sudomesh/disaster-radio/esp8266/esp8266_main.ino

#include <ESP8266WiFi.h>
#include <ESP8266mDNS.h>
#include <ArduinoOTA.h>
#include <FS.h>
#include <Hash.h>
#include <ESPAsyncTCP.h>
#include <ESPAsyncWebServer.h>
#include <SPIFFSEditor.h>
#include <SPI.h>
#include <LoRa.h>

// This is just a slightly modified version of the
// official ESPAsyncWebserver example
// Where SPI has been added to talk to an arduino running the
// arduino_spi_test code

// SKETCH BEGIN
AsyncWebServer server(80);
AsyncWebSocket ws("/ws");
AsyncEventSource events("/events");

void onWsEvent(AsyncWebSocket * server, AsyncWebSocketClient * client, AwsEventType type, void * arg, uint8_t *data, size_t len){
  if(type == WS_EVT_CONNECT){
    Serial.printf("ws[%s][%u] connect\n", server->url(), client->id());
    client->printf("Hello Client %u :)", client->id());
    client->ping();
  } else if(type == WS_EVT_DISCONNECT){
    Serial.printf("ws[%s][%u] disconnect: %u\n", server->url(), client->id());
  } else if(type == WS_EVT_ERROR){
    Serial.printf("ws[%s][%u] error(%u): %s\n", server->url(), client->id(), *((uint16_t*)arg), (char*)data);
  } else if(type == WS_EVT_PONG){
    Serial.printf("ws[%s][%u] pong[%u]: %s\n", server->url(), client->id(), len, (len)?(char*)data:"");
  } else if(type == WS_EVT_DATA){
    AwsFrameInfo * info = (AwsFrameInfo*)arg;
    String msg = "";
    if(info->final && info->index == 0 && info->len == len){
      //the whole message is in a single frame and we got all of it's data
      Serial.printf("ws[%s][%u] %s-message[%llu]: ", server->url(), client->id(), (info->opcode == WS_TEXT)?"text":"binary", info->len);

      if(info->opcode == WS_TEXT){
        for(size_t i=0; i < info->len; i++) {
          msg += (char) data[i];
        }
      } else {
        char buff[3];
        for(size_t i=0; i < info->len; i++) {
          sprintf(buff, "%02x ", (uint8_t) data[i]);
          msg += buff ;
        }
      }
      Serial.printf("%s\n",msg.c_str());

      if(info->opcode == WS_TEXT)
        client->text("I got your text message");
      else
        client->binary("I got your binary message");
    } else {
      //message is comprised of multiple frames or the frame is split into multiple packets
      if(info->index == 0){
        if(info->num == 0)
          Serial.printf("ws[%s][%u] %s-message start\n", server->url(), client->id(), (info->message_opcode == WS_TEXT)?"text":"binary");
        Serial.printf("ws[%s][%u] frame[%u] start[%llu]\n", server->url(), client->id(), info->num, info->len);
      }

      Serial.printf("ws[%s][%u] frame[%u] %s[%llu - %llu]: ", server->url(), client->id(), info->num, (info->message_opcode == WS_TEXT)?"text":"binary", info->index, info->index + len);

      if(info->opcode == WS_TEXT){
        for(size_t i=0; i < info->len; i++) {
          msg += (char) data[i];
        }
      } else {
        char buff[3];
        for(size_t i=0; i < info->len; i++) {
          sprintf(buff, "%02x ", (uint8_t) data[i]);
          msg += buff ;
        }
      }
      Serial.printf("%s\n",msg.c_str());

      if((info->index + len) == info->len){
        Serial.printf("ws[%s][%u] frame[%u] end[%llu]\n", server->url(), client->id(), info->num, info->len);
        if(info->final){
          Serial.printf("ws[%s][%u] %s-message end\n", server->url(), client->id(), (info->message_opcode == WS_TEXT)?"text":"binary");
          if(info->message_opcode == WS_TEXT)
            client->text("I got your text message");
          else
            client->binary("I got your binary message");
        }
      }
    }
  }
}


const char* ssid = "DisasterRadio duino";
//const char* password = "*******";
const char * hostName = "esp-async";
const char* http_username = "admin";
const char* http_password = "admin";

void setup(){
  Serial.begin(115200);
  Serial.setDebugOutput(true);
  WiFi.hostname(hostName);
  //WiFi.mode(WIFI_AP_STA);
  WiFi.mode(WIFI_AP);
  WiFi.softAP(ssid);
  /*
  WiFi.begin(ssid, password);
  if (WiFi.waitForConnectResult() != WL_CONNECTED) {
    Serial.printf("STA: Failed!\n");
    WiFi.disconnect(false);
    delay(1000);
    WiFi.begin(ssid, password);
  }
  */

  //Send OTA events to the browser
  ArduinoOTA.onStart([]() { events.send("Update Start", "ota"); });
  ArduinoOTA.onEnd([]() { events.send("Update End", "ota"); });
  ArduinoOTA.onProgress([](unsigned int progress, unsigned int total) {
    char p[32];
    sprintf(p, "Progress: %u%%\n", (progress/(total/100)));
    events.send(p, "ota");
  });
  ArduinoOTA.onError([](ota_error_t error) {
    if(error == OTA_AUTH_ERROR) events.send("Auth Failed", "ota");
    else if(error == OTA_BEGIN_ERROR) events.send("Begin Failed", "ota");
    else if(error == OTA_CONNECT_ERROR) events.send("Connect Failed", "ota");
    else if(error == OTA_RECEIVE_ERROR) events.send("Recieve Failed", "ota");
    else if(error == OTA_END_ERROR) events.send("End Failed", "ota");
  });
  ArduinoOTA.setHostname(hostName);
  ArduinoOTA.begin();

  MDNS.addService("http","tcp",80);

  SPIFFS.begin();

  ws.onEvent(onWsEvent);
  server.addHandler(&ws);

  events.onConnect([](AsyncEventSourceClient *client){
    client->send("hello!",NULL,millis(),1000);
  });
  server.addHandler(&events);

  server.addHandler(new SPIFFSEditor(http_username,http_password));

  server.on("/heap", HTTP_GET, [](AsyncWebServerRequest *request){
    request->send(200, "text/plain", String(ESP.getFreeHeap()));
  });

  server.serveStatic("/", SPIFFS, "/").setDefaultFile("index.htm");

  server.onNotFound([](AsyncWebServerRequest *request){
    Serial.printf("NOT_FOUND: ");
    if(request->method() == HTTP_GET)
      Serial.printf("GET");
    else if(request->method() == HTTP_POST)
      Serial.printf("POST");
    else if(request->method() == HTTP_DELETE)
      Serial.printf("DELETE");
    else if(request->method() == HTTP_PUT)
      Serial.printf("PUT");
    else if(request->method() == HTTP_PATCH)
      Serial.printf("PATCH");
    else if(request->method() == HTTP_HEAD)
      Serial.printf("HEAD");
    else if(request->method() == HTTP_OPTIONS)
      Serial.printf("OPTIONS");
    else
      Serial.printf("UNKNOWN");
    Serial.printf(" http://%s%s\n", request->host().c_str(), request->url().c_str());

    if(request->contentLength()){
      Serial.printf("_CONTENT_TYPE: %s\n", request->contentType().c_str());
      Serial.printf("_CONTENT_LENGTH: %u\n", request->contentLength());
    }

    int headers = request->headers();
    int i;
    for(i=0;i<headers;i++){
      AsyncWebHeader* h = request->getHeader(i);
      Serial.printf("_HEADER[%s]: %s\n", h->name().c_str(), h->value().c_str());
    }

    int params = request->params();
    for(i=0;i<params;i++){
      AsyncWebParameter* p = request->getParam(i);
      if(p->isFile()){
        Serial.printf("_FILE[%s]: %s, size: %u\n", p->name().c_str(), p->value().c_str(), p->size());
      } else if(p->isPost()){
        Serial.printf("_POST[%s]: %s\n", p->name().c_str(), p->value().c_str());
      } else {
        Serial.printf("_GET[%s]: %s\n", p->name().c_str(), p->value().c_str());
      }
    }

    request->send(404);
  });
  server.onFileUpload([](AsyncWebServerRequest *request, const String& filename, size_t index, uint8_t *data, size_t len, bool final){
    if(!index)
      Serial.printf("UploadStart: %s\n", filename.c_str());
    Serial.printf("%s", (const char*)data);
    if(final)
      Serial.printf("UploadEnd: %s (%u)\n", filename.c_str(), index+len);
  });
  server.onRequestBody([](AsyncWebServerRequest *request, uint8_t *data, size_t len, size_t index, size_t total){
    if(!index)
      Serial.printf("BodyStart: %u\n", total);
    Serial.printf("%s", (const char*)data);
    if(index + len == total)
      Serial.printf("BodyEnd: %u\n", total);
  });
  server.begin();


  digitalWrite(SS, HIGH);
  SPI.begin();
  SPI.setFrequency(50000);
}

int mcount = 0;
int ecount = 0;
char last = 0;
void loop(){
  ArduinoOTA.handle();

  char c;
  char b;

  // enable Slave Select
  digitalWrite(SS, LOW);    // SS is pin 10

  // send test string
  for (const char * p = "Hello, world!\n" ; c = *p; p++) {
    b = SPI.transfer (c);
    mcount++;
    delayMicroseconds (100);
    if(b > 1 && (b != (last + 1))) {
    
      ecount++;
    }
    if(b == 0) {
      ecount++;
    }
    
    last = b;
  }
  if(mcount >= 2000) {
    Serial.printf("tick: %d, %d\n", mcount, ecount);
    mcount = 0;
    ecount = 0;
  }
  // disable Slave Select
  digitalWrite(SS, HIGH);

}
