sudomesh/disaster-radio/firmware/src/DisasterServer.h

#ifndef DISASTERSERVER_H
#define DISASTERSERVER_H

#ifndef SIM
#include <Arduino.h>
#endif
#include <cstddef>
#include <LoRaLayer2.h>

#include "DisasterClient.h"

class DisasterClient;

class DisasterServer
{
public:
    virtual DisasterClient* connect(DisasterClient *client) = 0;
    virtual void disconnect(DisasterClient *client) = 0;

    virtual void setup() = 0;
    virtual void loop() = 0;

    virtual void transmit(DisasterClient *client, struct Datagram datagram, size_t len) = 0;
};

#endif
