sudomesh/disaster-radio/firmware/src/client/TCPClient.cpp

#include "TCPClient.h"
#include <LoRaLayer2.h>

void TCPClient::receive(struct Datagram datagram, size_t len)
{
    client->add((char *)datagram.message, len - DATAGRAM_HEADER);
    client->send();
}

void TCPClient::handleData(void *data, size_t len)
{
  struct Datagram datagram;
  memcpy(datagram.destination, BROADCAST, ADDR_LENGTH);
  datagram.type = 'c';
  memcpy(datagram.message, data, len);
  len = len+DATAGRAM_HEADER;
  server->transmit(this, datagram, len);
}

void TCPClient::handleDisconnect()
{
  server->disconnect(this);
}

void TCPClient::handleError(int8_t error)
{
  server->disconnect(this);
}

void TCPClient::handleTimeout(uint32_t time)
{
  server->disconnect(this);
}

void TCPClient::startServer(AsyncServer *server, void (*callback)(TCPClient *))
{
  server->onClient([callback](void *arg, AsyncClient *client) {
    // add to clients list
    TCPClient *tcp_client = new TCPClient(client);

    // register events
    client->onData([tcp_client](void *arg, AsyncClient *client, void *data, size_t len) {
        tcp_client->handleData(data, len);
    });
    client->onDisconnect([tcp_client](void *arg, AsyncClient *client) {
        tcp_client->handleDisconnect();
    });
    client->onError([tcp_client](void *arg, AsyncClient *client, int8_t error) {
        tcp_client->handleError(error);
    });
    client->onTimeout([tcp_client](void *arg, AsyncClient *client, uint32_t time) {
        tcp_client->handleTimeout(time);
    });

    callback(tcp_client);
  },
                   NULL);
  server->begin();
}
