sudomesh/disaster-radio/firmware/src/DisasterHistory.h

#ifndef DISASTERHISTORY_H
#define DISASTERHISTORY_H

#include "DisasterClient.h"

class DisasterHistory
{
public:
    virtual void record(struct Datagram datagram, size_t len) = 0;
    virtual void replay(DisasterClient *client) = 0;
};

#endif
