sudomesh/disaster-radio/firmware/src/history/HistorySD.h

#ifndef HISTORYSDCLIENT_CPP
#define HISTORYSDCLIENT_CPP

#include "../DisasterClient.h"
#include "../DisasterHistory.h"

#include <SPI.h>

class HistorySD : public DisasterHistory
{
    bool initialized = false;
    const char *log_path = "/log.txt";
    SPIClass *sd;

public:
    HistorySD(SPIClass *s)
        : sd{s} {};

    bool init();
    void record(struct Datagram datagram, size_t len);
    void replay(DisasterClient *client);
};

#endif
